e-nano/open-ndvi-handheld/firmware/src/as7265x_calibration_data.h

#pragma once

#include <Arduino.h>

static constexpr size_t AS7265X_CHANNEL_COUNT = 18;
static constexpr size_t AS7265X_CAL_POINT_COUNT = 6;

// Each row is one wavelength channel, ordered as:
// 410, 435, 460, 485, 510, 535, 560, 585, 610, 645, 680, 705, 730, 760, 810, 860, 900, 940 nm

#define AS7265X_DEFAULT_INPUT_ROW { \
  0.000000f, 0.200000f, 0.400000f, \
  0.600000f, 0.800000f, 1.000000f \
}

#define AS7265X_DEFAULT_FACTOR_ROW { \
  1.000000f, 1.000000f, 1.000000f, \
  1.000000f, 1.000000f, 1.000000f \
}

static float UP_CAL_INPUTS[AS7265X_CHANNEL_COUNT][AS7265X_CAL_POINT_COUNT] = {
  AS7265X_DEFAULT_INPUT_ROW,
  AS7265X_DEFAULT_INPUT_ROW,
  AS7265X_DEFAULT_INPUT_ROW,
  AS7265X_DEFAULT_INPUT_ROW,
  AS7265X_DEFAULT_INPUT_ROW,
  AS7265X_DEFAULT_INPUT_ROW,
  AS7265X_DEFAULT_INPUT_ROW,
  AS7265X_DEFAULT_INPUT_ROW,
  AS7265X_DEFAULT_INPUT_ROW,
  AS7265X_DEFAULT_INPUT_ROW,
  AS7265X_DEFAULT_INPUT_ROW,
  AS7265X_DEFAULT_INPUT_ROW,
  AS7265X_DEFAULT_INPUT_ROW,
  AS7265X_DEFAULT_INPUT_ROW,
  AS7265X_DEFAULT_INPUT_ROW,
  AS7265X_DEFAULT_INPUT_ROW,
  AS7265X_DEFAULT_INPUT_ROW,
  AS7265X_DEFAULT_INPUT_ROW,
};

static float UP_CAL_FACTORS[AS7265X_CHANNEL_COUNT][AS7265X_CAL_POINT_COUNT] = {
  AS7265X_DEFAULT_FACTOR_ROW,
  AS7265X_DEFAULT_FACTOR_ROW,
  AS7265X_DEFAULT_FACTOR_ROW,
  AS7265X_DEFAULT_FACTOR_ROW,
  AS7265X_DEFAULT_FACTOR_ROW,
  AS7265X_DEFAULT_FACTOR_ROW,
  AS7265X_DEFAULT_FACTOR_ROW,
  AS7265X_DEFAULT_FACTOR_ROW,
  AS7265X_DEFAULT_FACTOR_ROW,
  AS7265X_DEFAULT_FACTOR_ROW,
  AS7265X_DEFAULT_FACTOR_ROW,
  AS7265X_DEFAULT_FACTOR_ROW,
  AS7265X_DEFAULT_FACTOR_ROW,
  AS7265X_DEFAULT_FACTOR_ROW,
  AS7265X_DEFAULT_FACTOR_ROW,
  AS7265X_DEFAULT_FACTOR_ROW,
  AS7265X_DEFAULT_FACTOR_ROW,
  AS7265X_DEFAULT_FACTOR_ROW,
};

static float DOWN_CAL_INPUTS[AS7265X_CHANNEL_COUNT][AS7265X_CAL_POINT_COUNT] = {
  AS7265X_DEFAULT_INPUT_ROW,
  AS7265X_DEFAULT_INPUT_ROW,
  AS7265X_DEFAULT_INPUT_ROW,
  AS7265X_DEFAULT_INPUT_ROW,
  AS7265X_DEFAULT_INPUT_ROW,
  AS7265X_DEFAULT_INPUT_ROW,
  AS7265X_DEFAULT_INPUT_ROW,
  AS7265X_DEFAULT_INPUT_ROW,
  AS7265X_DEFAULT_INPUT_ROW,
  AS7265X_DEFAULT_INPUT_ROW,
  AS7265X_DEFAULT_INPUT_ROW,
  AS7265X_DEFAULT_INPUT_ROW,
  AS7265X_DEFAULT_INPUT_ROW,
  AS7265X_DEFAULT_INPUT_ROW,
  AS7265X_DEFAULT_INPUT_ROW,
  AS7265X_DEFAULT_INPUT_ROW,
  AS7265X_DEFAULT_INPUT_ROW,
  AS7265X_DEFAULT_INPUT_ROW,
};

static float DOWN_CAL_FACTORS[AS7265X_CHANNEL_COUNT][AS7265X_CAL_POINT_COUNT] = {
  AS7265X_DEFAULT_FACTOR_ROW,
  AS7265X_DEFAULT_FACTOR_ROW,
  AS7265X_DEFAULT_FACTOR_ROW,
  AS7265X_DEFAULT_FACTOR_ROW,
  AS7265X_DEFAULT_FACTOR_ROW,
  AS7265X_DEFAULT_FACTOR_ROW,
  AS7265X_DEFAULT_FACTOR_ROW,
  AS7265X_DEFAULT_FACTOR_ROW,
  AS7265X_DEFAULT_FACTOR_ROW,
  AS7265X_DEFAULT_FACTOR_ROW,
  AS7265X_DEFAULT_FACTOR_ROW,
  AS7265X_DEFAULT_FACTOR_ROW,
  AS7265X_DEFAULT_FACTOR_ROW,
  AS7265X_DEFAULT_FACTOR_ROW,
  AS7265X_DEFAULT_FACTOR_ROW,
  AS7265X_DEFAULT_FACTOR_ROW,
  AS7265X_DEFAULT_FACTOR_ROW,
  AS7265X_DEFAULT_FACTOR_ROW,
};

#undef AS7265X_DEFAULT_INPUT_ROW
#undef AS7265X_DEFAULT_FACTOR_ROW
